RoBorregos/robocup-home/catkin_home/known_people/1.png

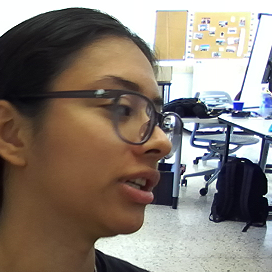
catkin_home/known_people/1.png
