RoBorregos/robocup-home/catkin_home/known_people/a0.png

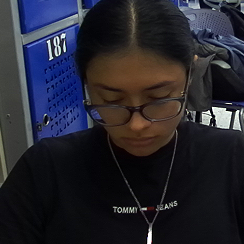
catkin_home/known_people/a0.png
