RoBorregos/robocup-home/catkin_home/known_people/adan.png

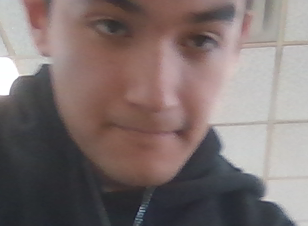
catkin_home/known_people/adan.png
