RoBorregos/robocup-home/catkin_home/known_people/ale0.png

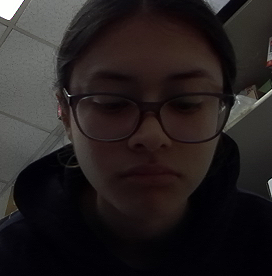
catkin_home/known_people/ale0.png
