RoBorregos/robocup-home/catkin_home/known_people/emiliano1.png

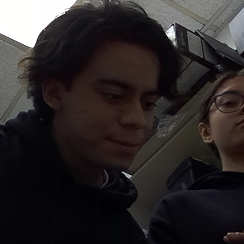
catkin_home/known_people/emiliano1.png
