RoBorregos/robocup-home/catkin_home/known_people/face0.png

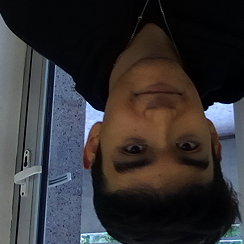
catkin_home/known_people/face0.png
