RoBorregos/robocup-home/catkin_home/known_people/face4.png

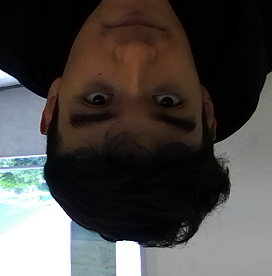
catkin_home/known_people/face4.png
