RoBorregos/robocup-home/catkin_home/known_people/iva0.png

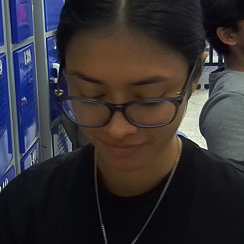
catkin_home/known_people/iva0.png
