RoBorregos/robocup-home/catkin_home/known_people/ivan0.png

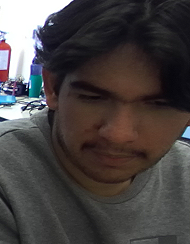
catkin_home/known_people/ivan0.png
