RoBorregos/robocup-home/catkin_home/known_people/random.png

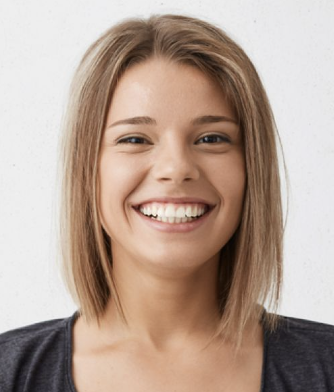
catkin_home/known_people/random.png
