RoBorregos/robocup-home/clusters.png

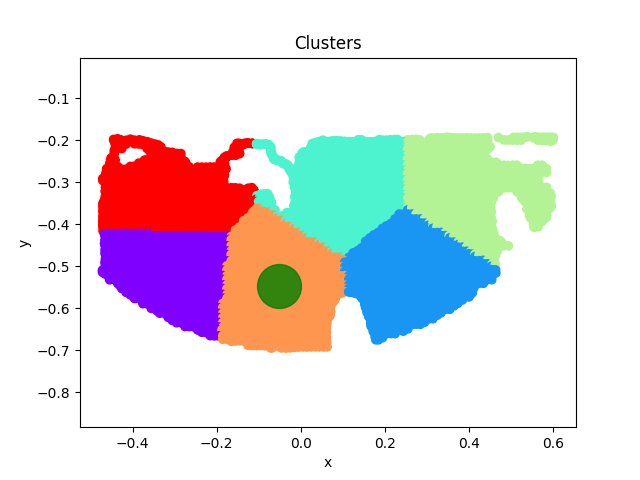
clusters.png
