RoBorregos/robocup-home/catkin_home/src/robot_description/meshes/GripperSF/Base_Gripper.STL

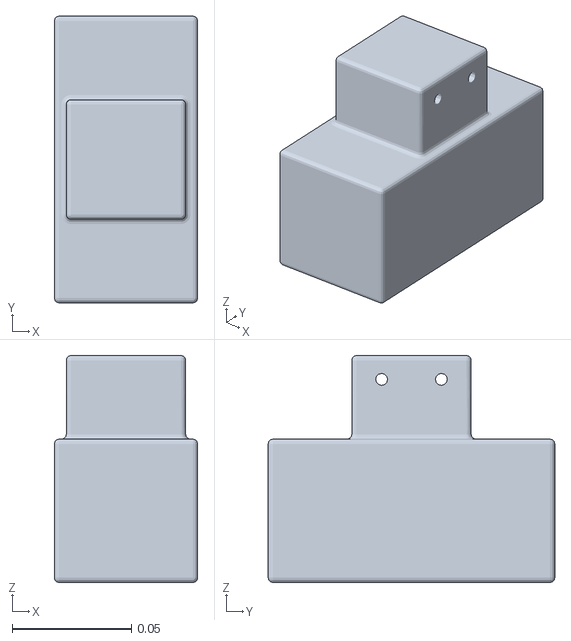
[picture p31: CAD file, 2023-06-28]
catkin_home/src/robot_description/meshes/GripperSF/Base_Gripper.STL
0.06 x 0.12 x 0.095
