RoBorregos/robocup-home/catkin_home/src/robot_description/meshes/Dashgo/BaseSinPalo.stl

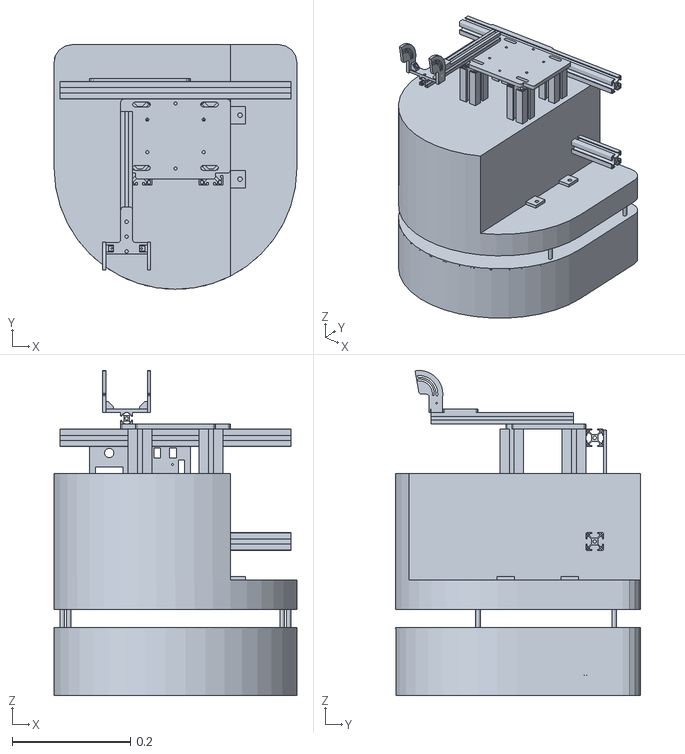
[picture p32: CAD file, 2023-11-25]
catkin_home/src/robot_description/meshes/Dashgo/BaseSinPalo.stl
0.41 x 0.413 x 0.549
