RoBorregos/robocup-home/catkin_home/src/robot_description/meshes/Garra_I.STL

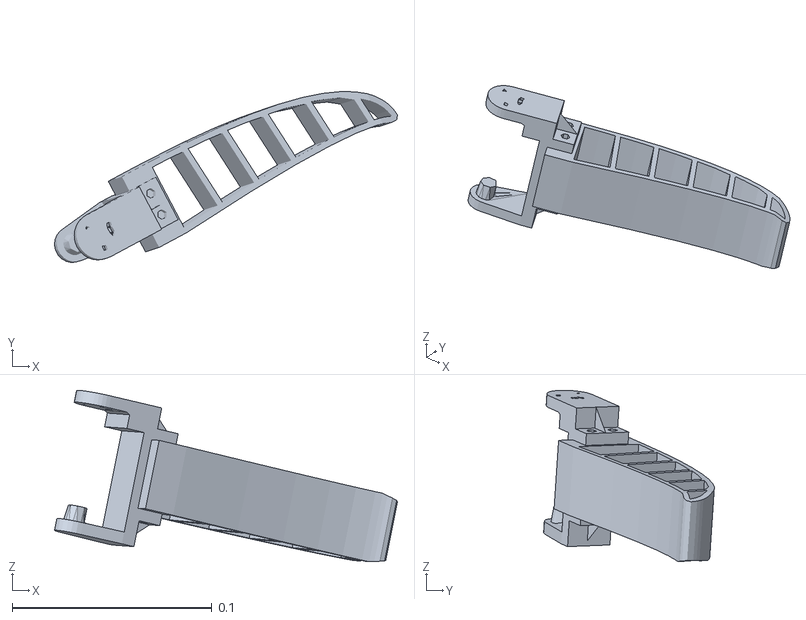
[picture p33: CAD file, 2022-05-05]
catkin_home/src/robot_description/meshes/Garra_I.STL
0.172 x 0.0855 x 0.0858
