RoBorregos/robocup-home/catkin_home/src/robot_description/meshes/BASE_PINZA.STL

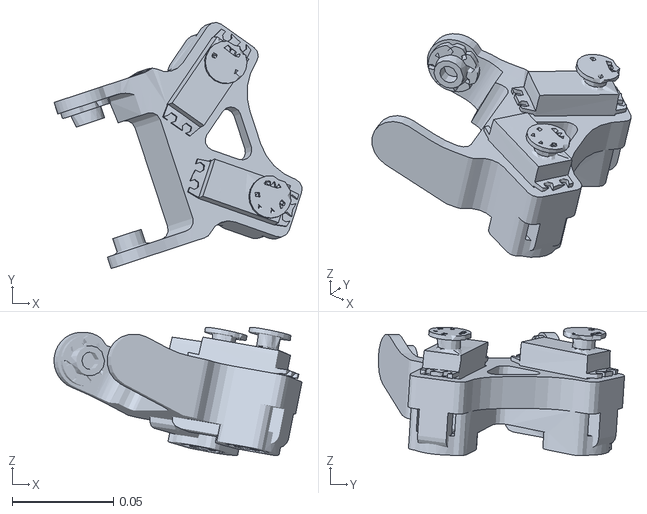
[picture p34: CAD file, 2022-05-05]
catkin_home/src/robot_description/meshes/BASE_PINZA.STL
0.123 x 0.122 x 0.0635
