RoBorregos/robocup-home/catkin_home/src/robot_description/meshes/Dashgo/BaseCollisionsSinPalo.stl

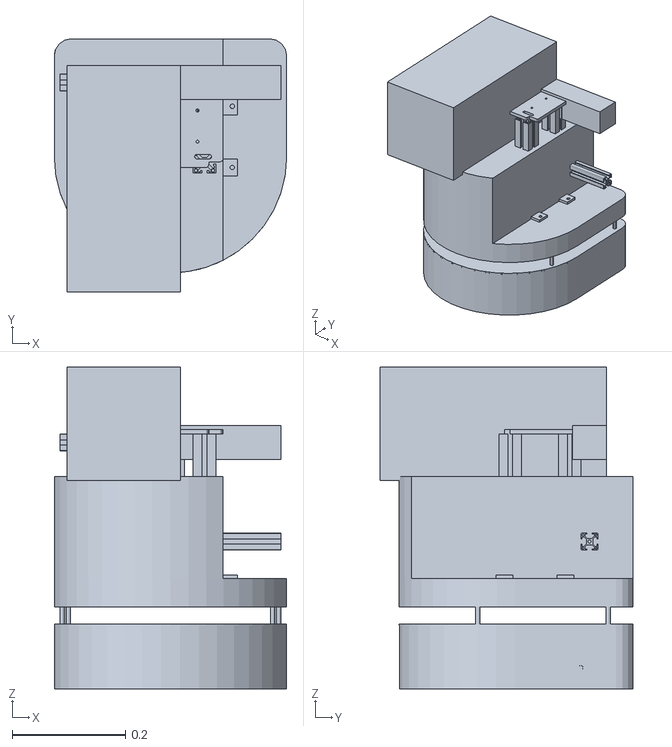
[picture p35: CAD file, 2023-11-25]
catkin_home/src/robot_description/meshes/Dashgo/BaseCollisionsSinPalo.stl
0.41 x 0.447 x 0.568
