RoBorregos/robocup-home/object_detection/images/test/IMG_9574.jpg

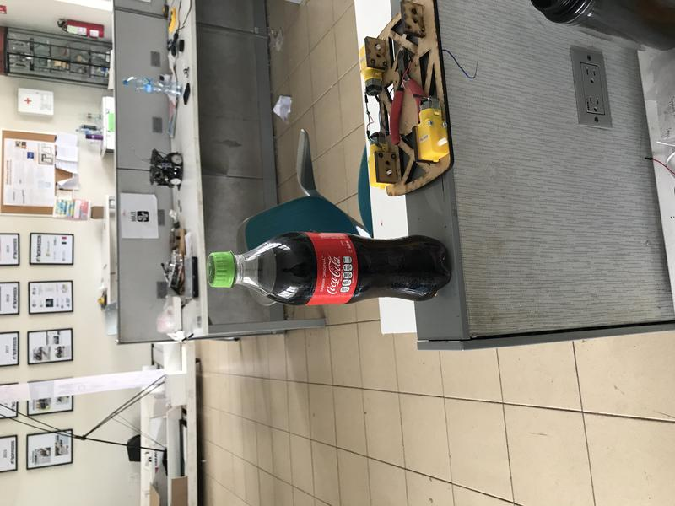
object_detection/images/test/IMG_9574.jpg
