RoBorregos/robocup-home/object_detection/images/test/IMG_9580.jpg

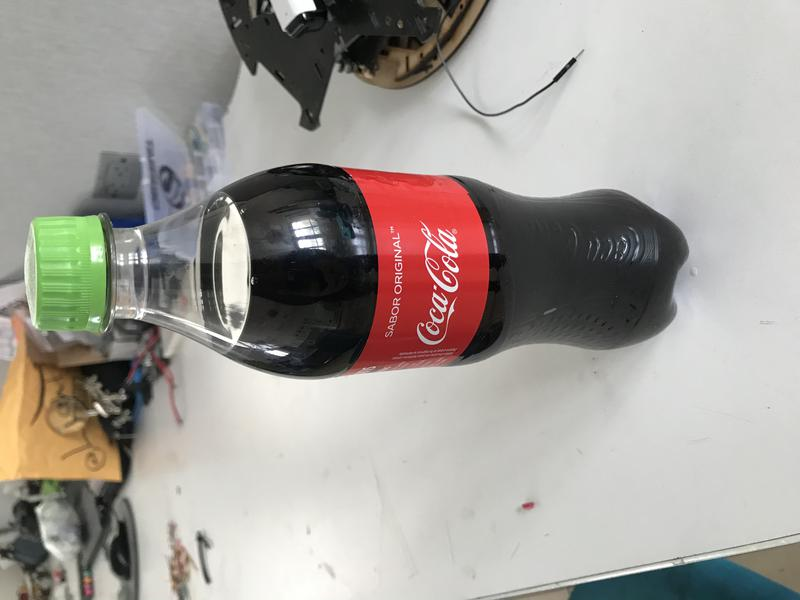
object_detection/images/test/IMG_9580.jpg
