RoBorregos/robocup-home/object_detection/images/test/IMG_9582.jpg

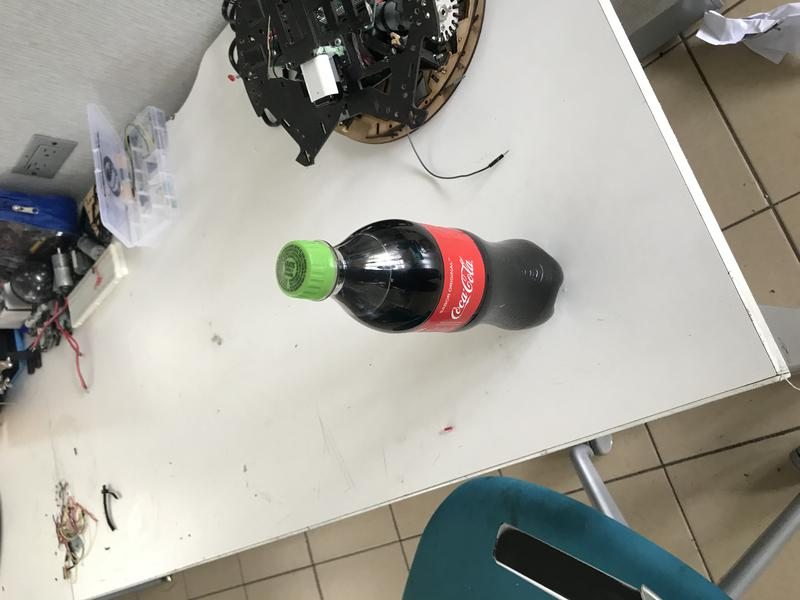
object_detection/images/test/IMG_9582.jpg
