RoBorregos/robocup-home/object_detection/images/test/IMG_9587.jpg

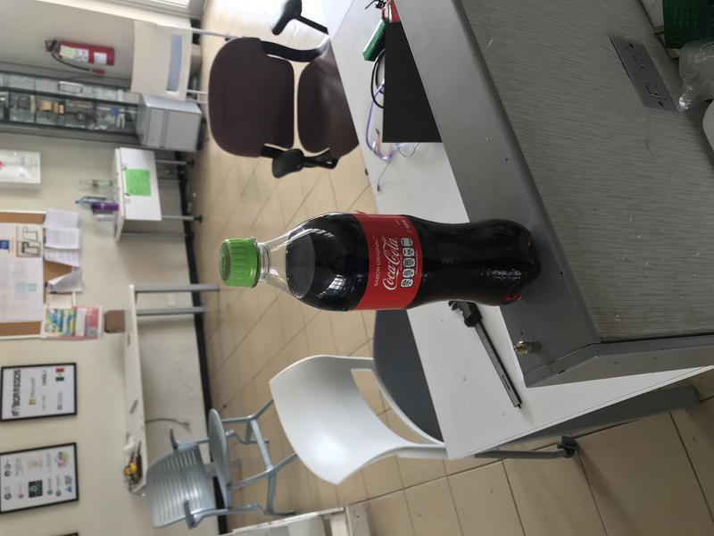
object_detection/images/test/IMG_9587.jpg
