RoBorregos/robocup-home/object_detection/images/test/IMG_9591.jpg

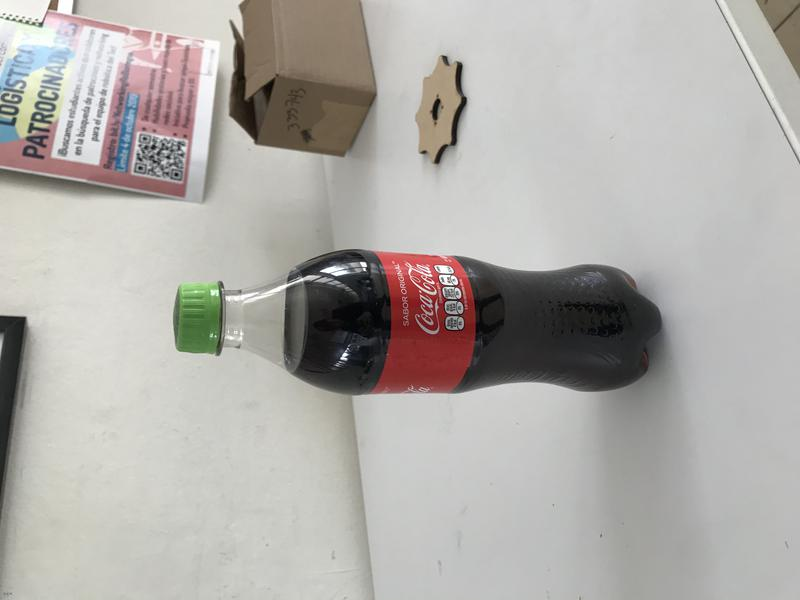
object_detection/images/test/IMG_9591.jpg
