RoBorregos/robocup-home/object_detection/images/test/IMG_9599.jpg

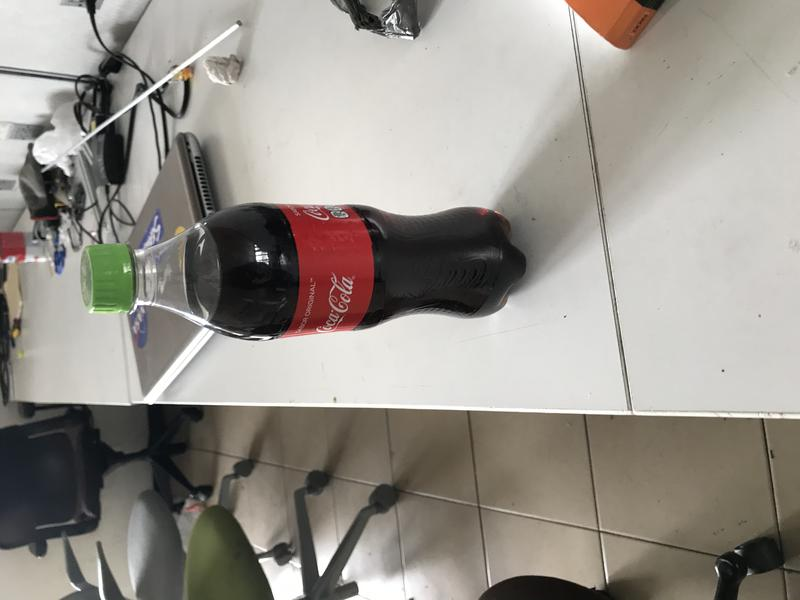
object_detection/images/test/IMG_9599.jpg
