RoBorregos/robocup-home/object_detection/images/test/IMG_9605.jpg

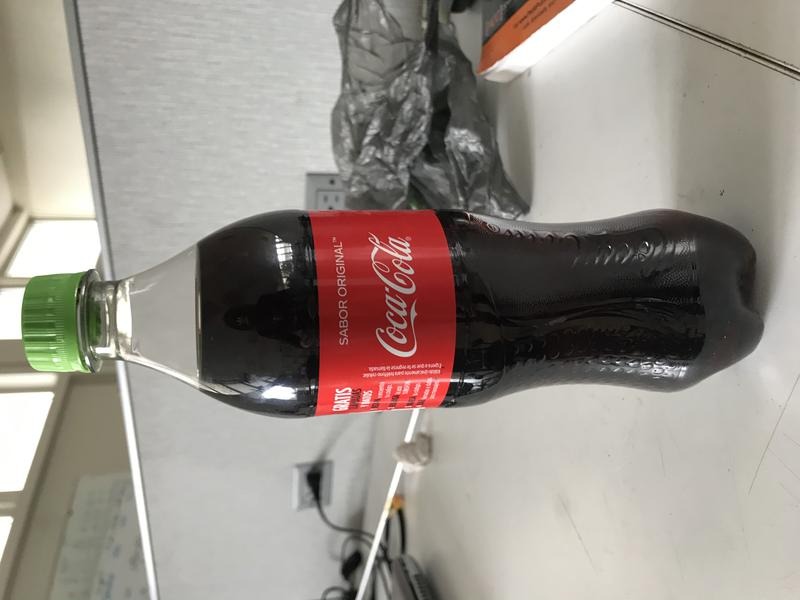
object_detection/images/test/IMG_9605.jpg
