RoBorregos/robocup-home/object_detection/images/test/IMG_9612.jpg

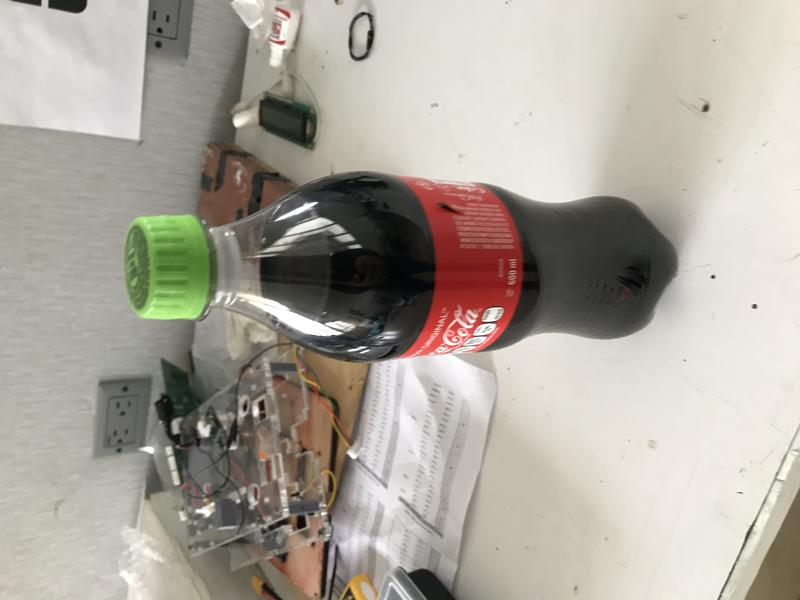
object_detection/images/test/IMG_9612.jpg
