RoBorregos/robocup-home/object_detection/images/test/IMG_9617.jpg

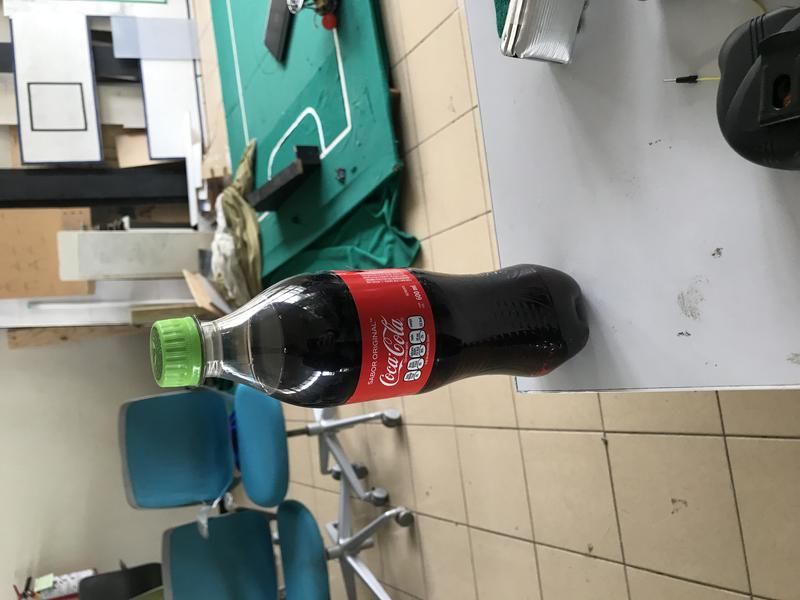
object_detection/images/test/IMG_9617.jpg
