RoBorregos/robocup-home/object_detection/images/test/IMG_9623.jpg

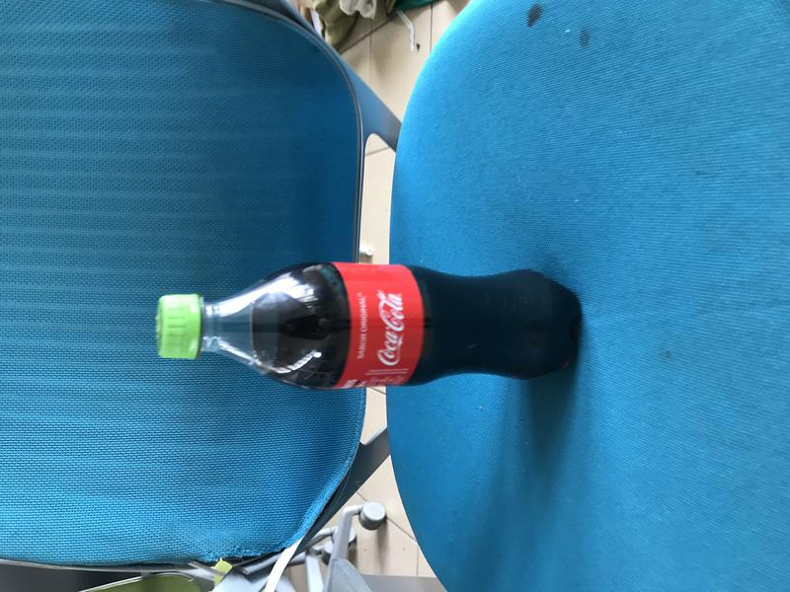
object_detection/images/test/IMG_9623.jpg
