RoBorregos/robocup-home/object_detection/images/test/IMG_9628.jpg

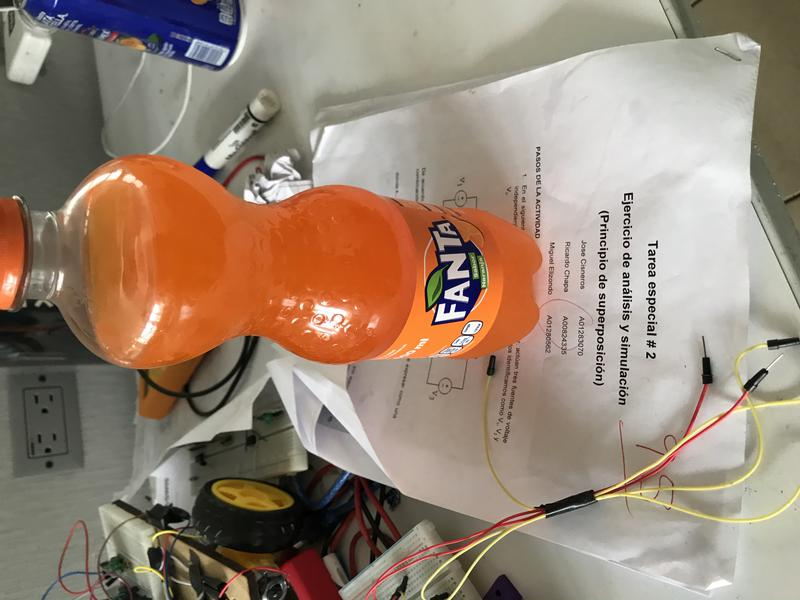
object_detection/images/test/IMG_9628.jpg
