RoBorregos/robocup-home/object_detection/images/test/IMG_9636.jpg

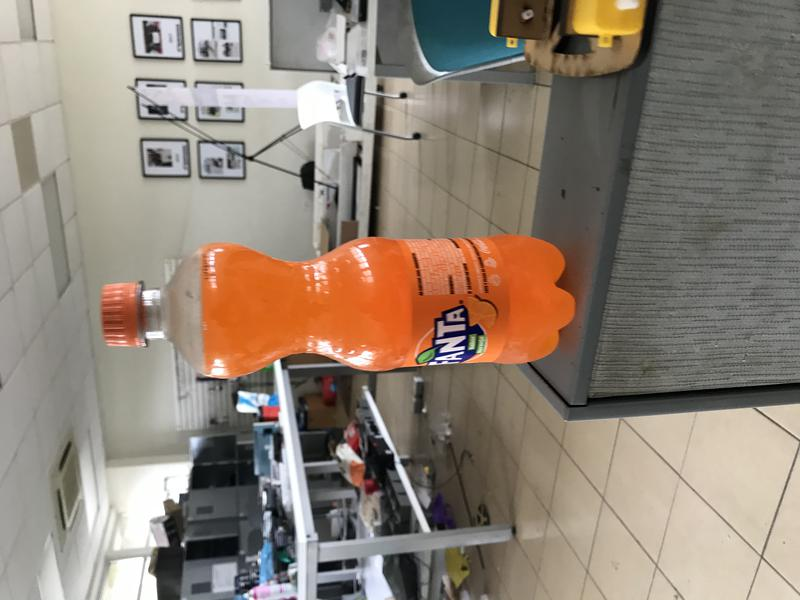
object_detection/images/test/IMG_9636.jpg
