RoBorregos/robocup-home/object_detection/images/test/IMG_9645.jpg

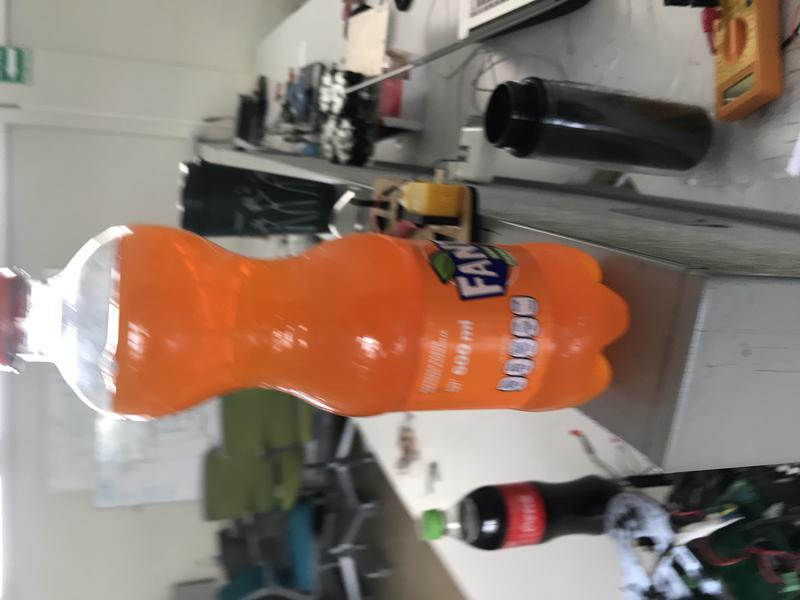
object_detection/images/test/IMG_9645.jpg
