RoBorregos/robocup-home/object_detection/images/test/IMG_9652.jpg

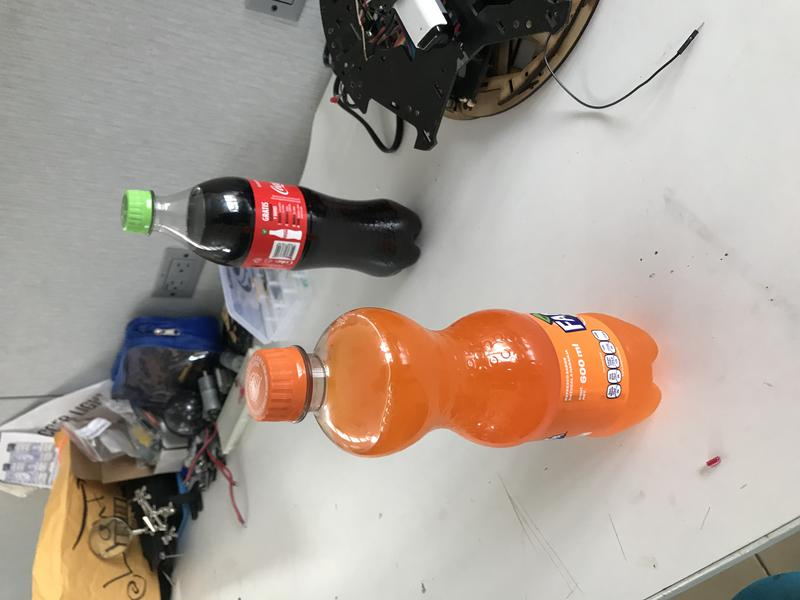
object_detection/images/test/IMG_9652.jpg
