RoBorregos/robocup-home/object_detection/images/test/IMG_9660.jpg

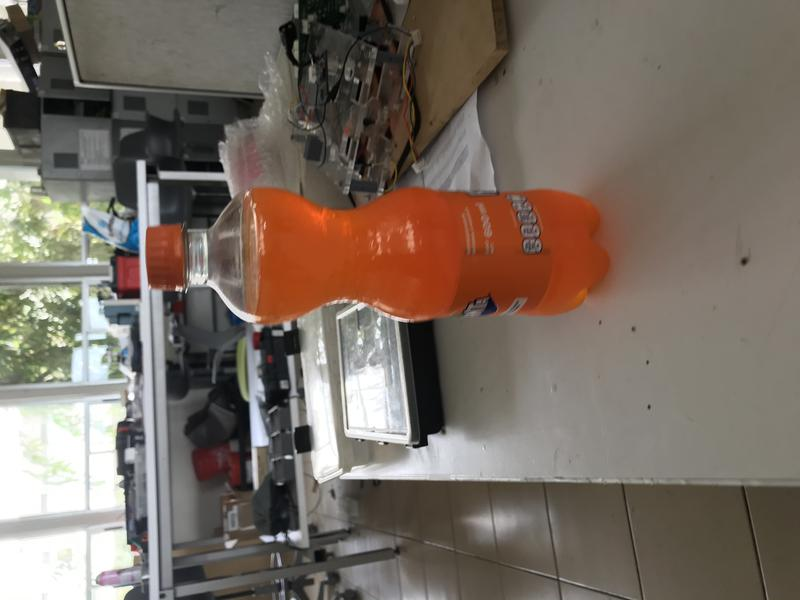
object_detection/images/test/IMG_9660.jpg
