RoBorregos/robocup-home/object_detection/images/test/IMG_9667.jpg

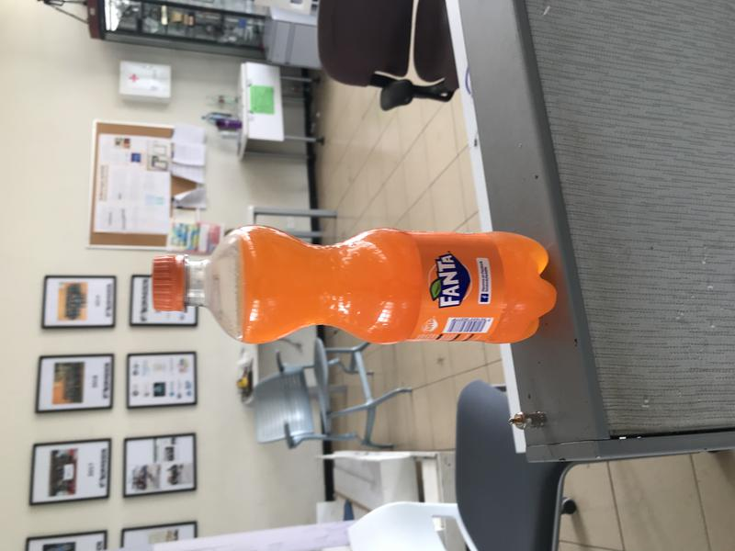
object_detection/images/test/IMG_9667.jpg
