RoBorregos/robocup-home/object_detection/images/test/IMG_9672.jpg

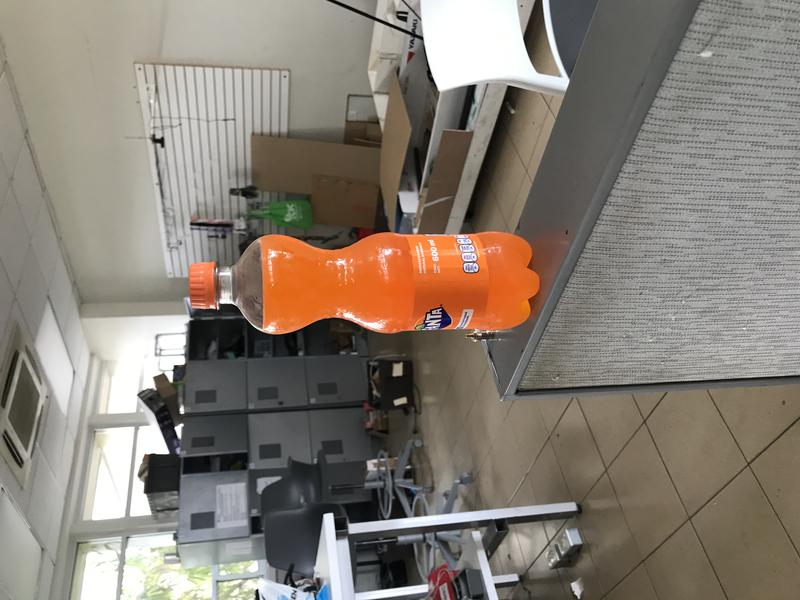
object_detection/images/test/IMG_9672.jpg
