RoBorregos/robocup-home/object_detection/images/test/IMG_9680.jpg

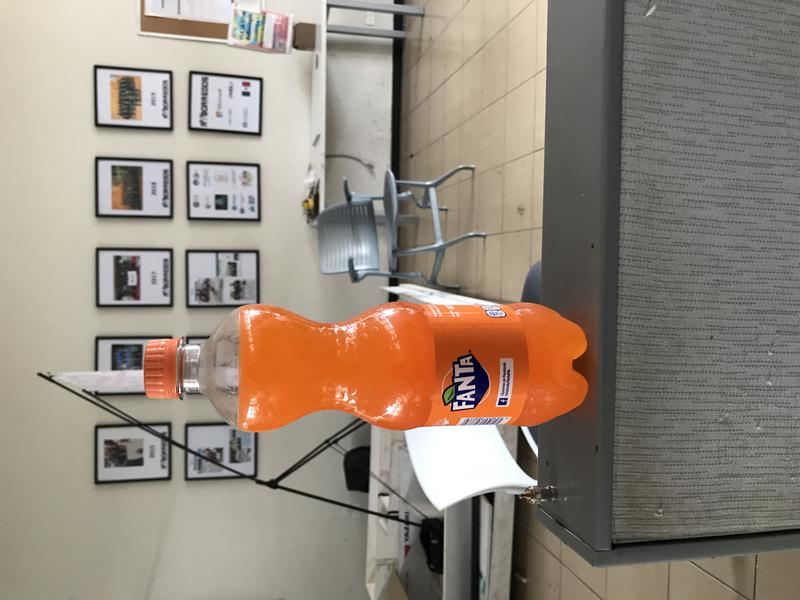
object_detection/images/test/IMG_9680.jpg
