RoBorregos/robocup-home/object_detection/images/test/IMG_9692.jpg

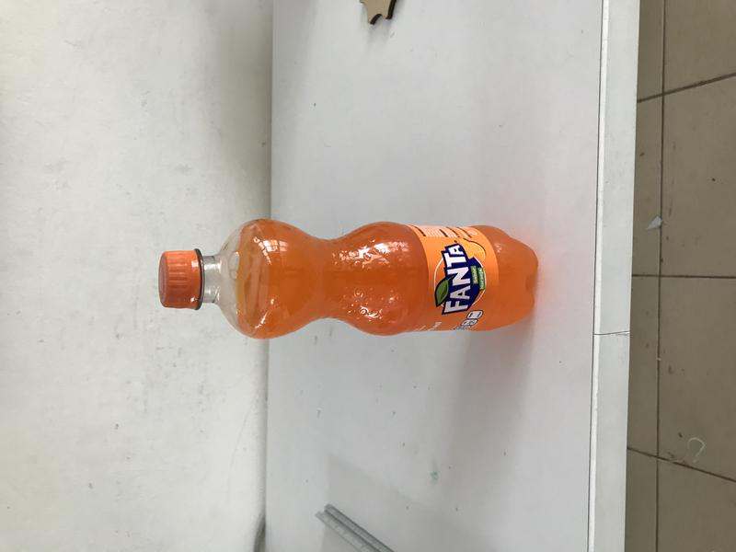
object_detection/images/test/IMG_9692.jpg
