RoBorregos/robocup-home/object_detection/images/test/IMG_9703.jpg

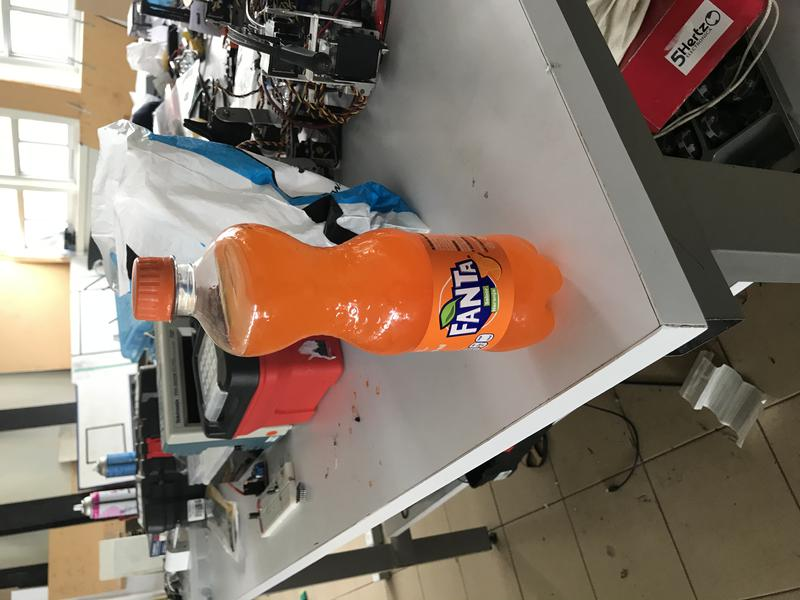
object_detection/images/test/IMG_9703.jpg
