RoBorregos/robocup-home/object_detection/images/test/IMG_9719.jpg

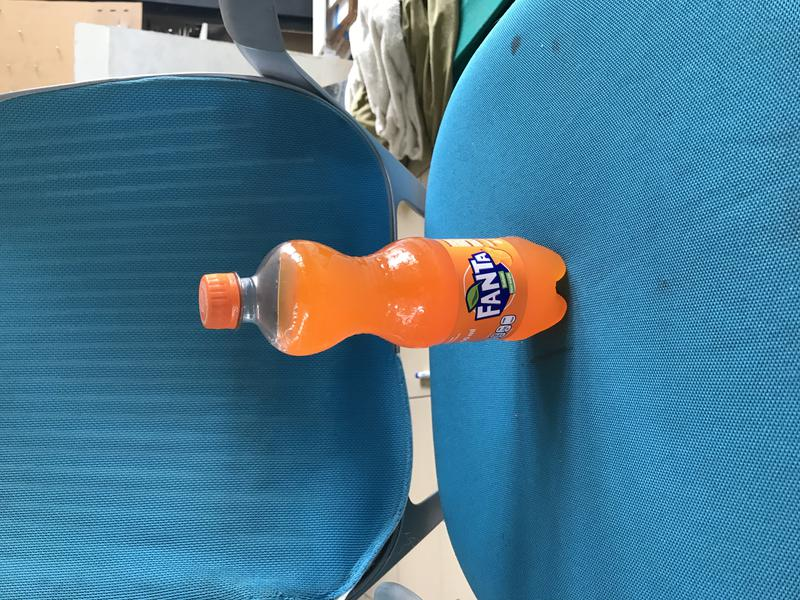
object_detection/images/test/IMG_9719.jpg
