RoBorregos/robocup-home/object_detection/images/test/IMG_9730.jpg

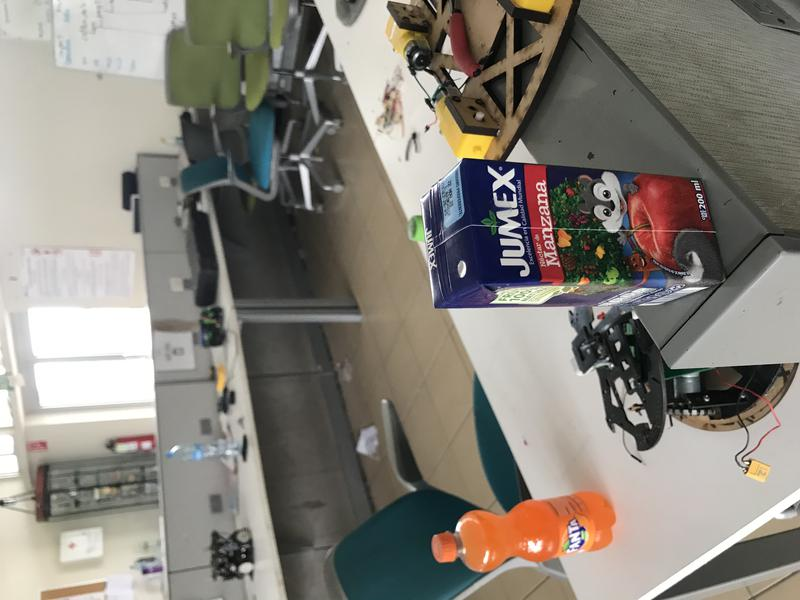
object_detection/images/test/IMG_9730.jpg
