RoBorregos/robocup-home/object_detection/images/test/IMG_9737.jpg

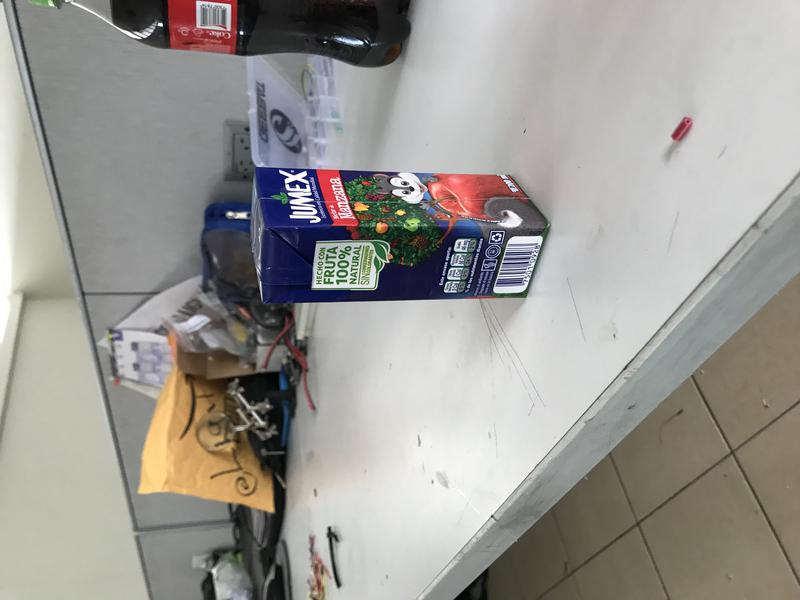
object_detection/images/test/IMG_9737.jpg
