RoBorregos/robocup-home/object_detection/images/test/IMG_9745.jpg

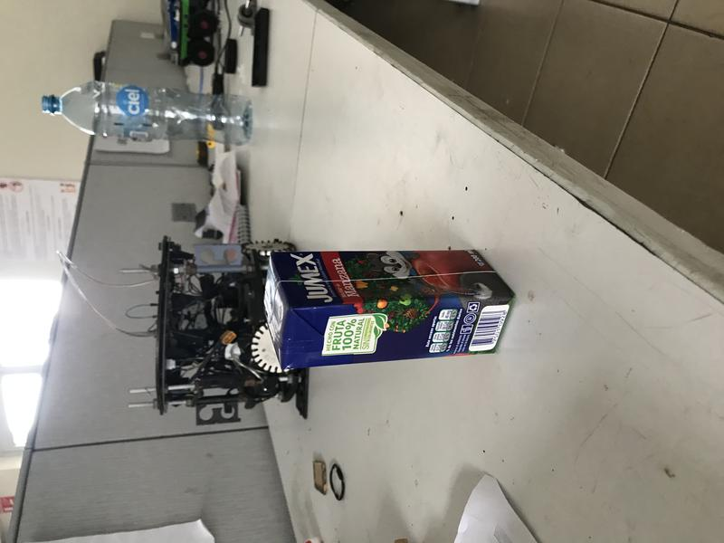
object_detection/images/test/IMG_9745.jpg
