RoBorregos/robocup-home/object_detection/images/test/IMG_9752.jpg

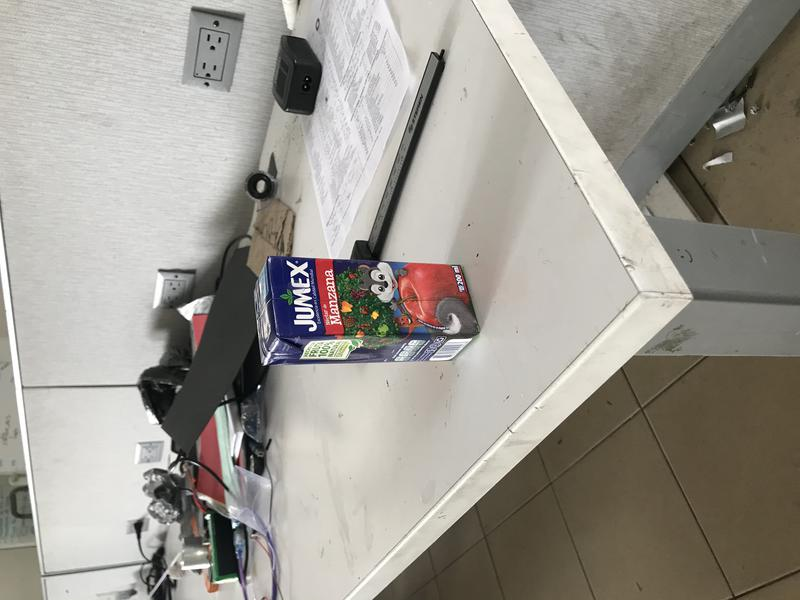
object_detection/images/test/IMG_9752.jpg
