RoBorregos/robocup-home/object_detection/images/test/IMG_9754.jpg

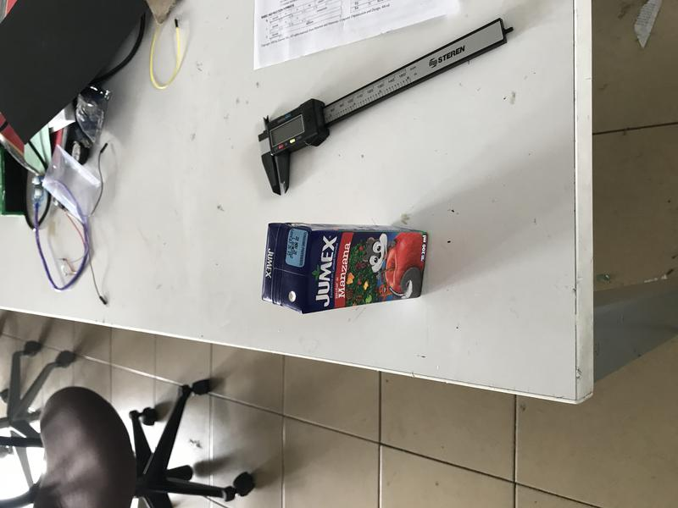
object_detection/images/test/IMG_9754.jpg
