RoBorregos/robocup-home/object_detection/images/test/IMG_9758.jpg

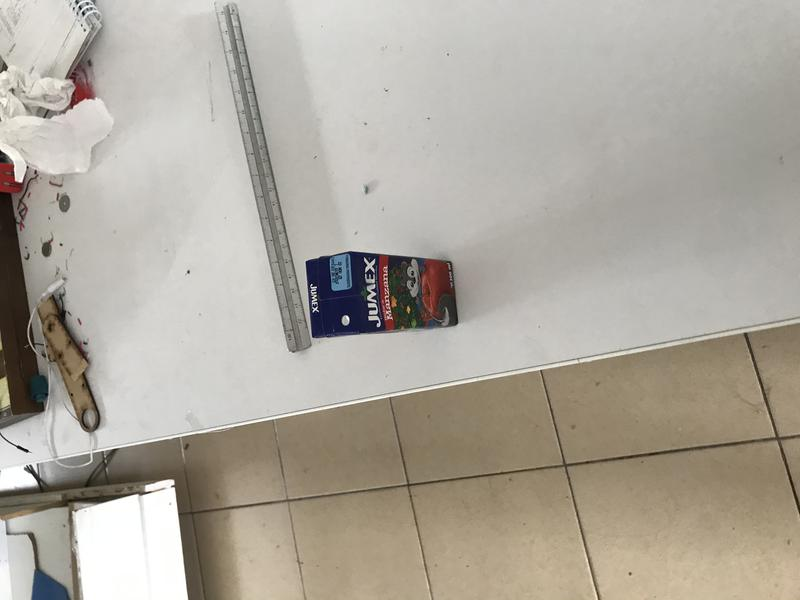
object_detection/images/test/IMG_9758.jpg
