RoBorregos/robocup-home/object_detection/images/test/IMG_9762.jpg

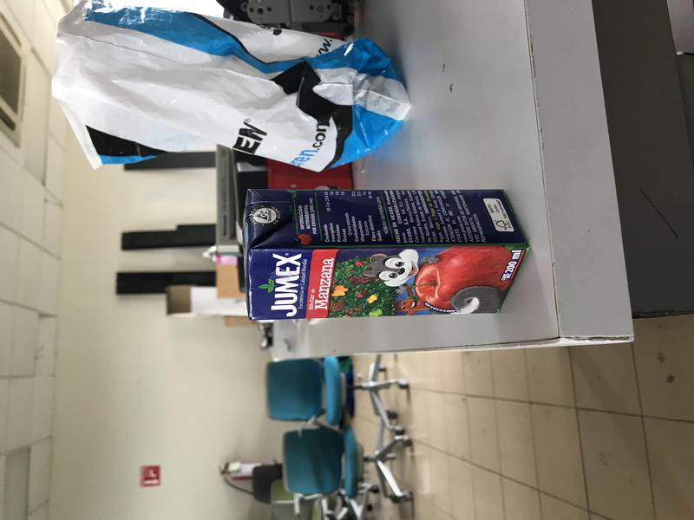
object_detection/images/test/IMG_9762.jpg
