RoBorregos/robocup-home/object_detection/images/test/IMG_9765.jpg

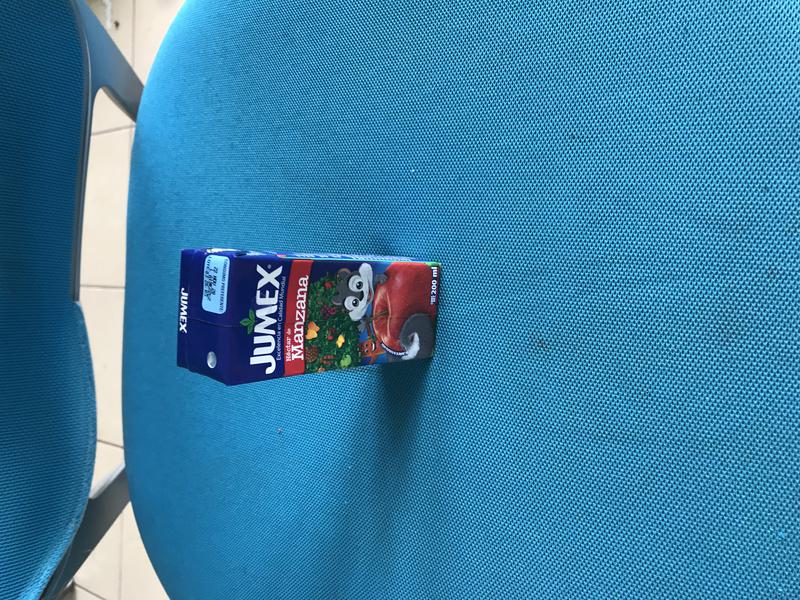
object_detection/images/test/IMG_9765.jpg
