RoBorregos/robocup-home/object_detection/images/test/IMG_9771.jpg

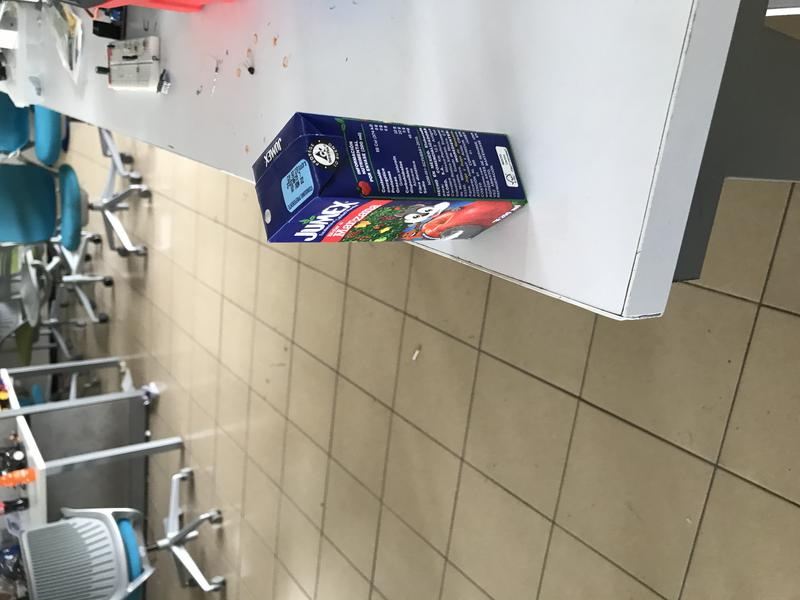
object_detection/images/test/IMG_9771.jpg
