RoBorregos/robocup-home/object_detection/images/test/IMG_9773.jpg

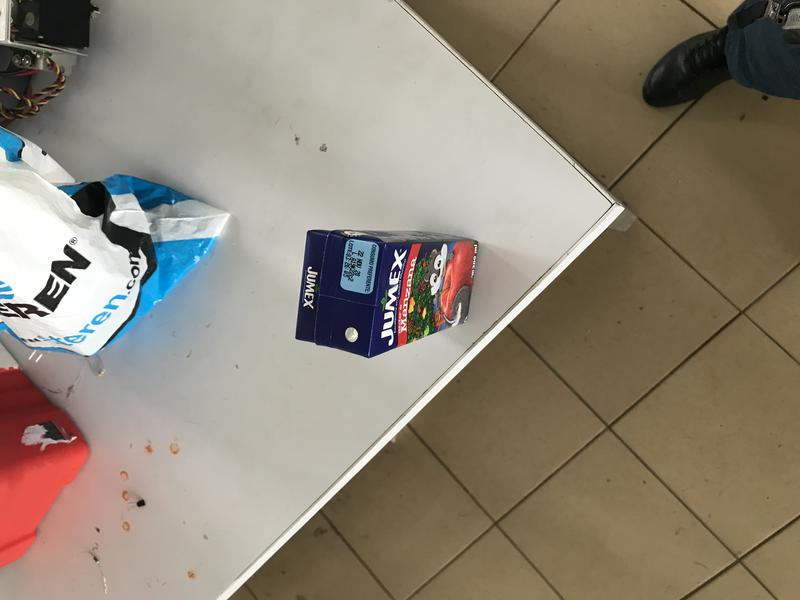
object_detection/images/test/IMG_9773.jpg
