RoBorregos/robocup-home/object_detection/images/test/IMG_9781.jpg

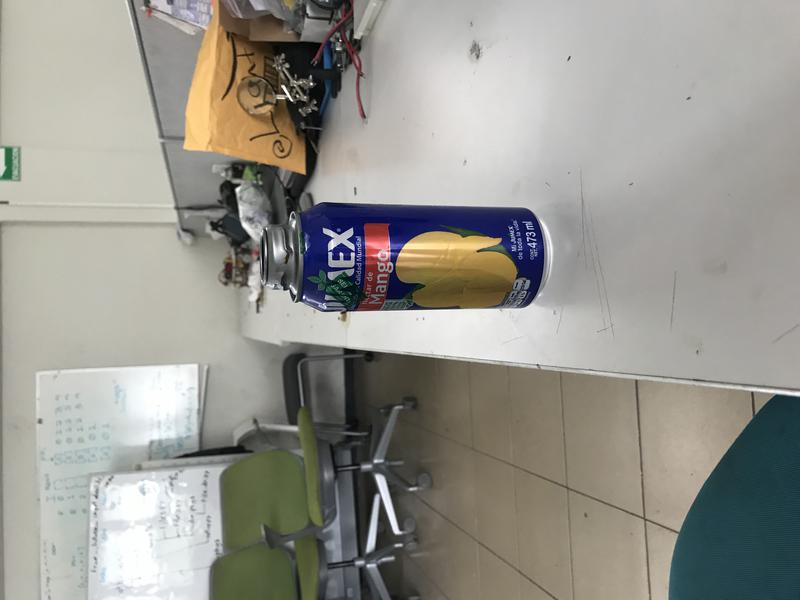
object_detection/images/test/IMG_9781.jpg
