RoBorregos/robocup-home/object_detection/images/test/IMG_9785.jpg

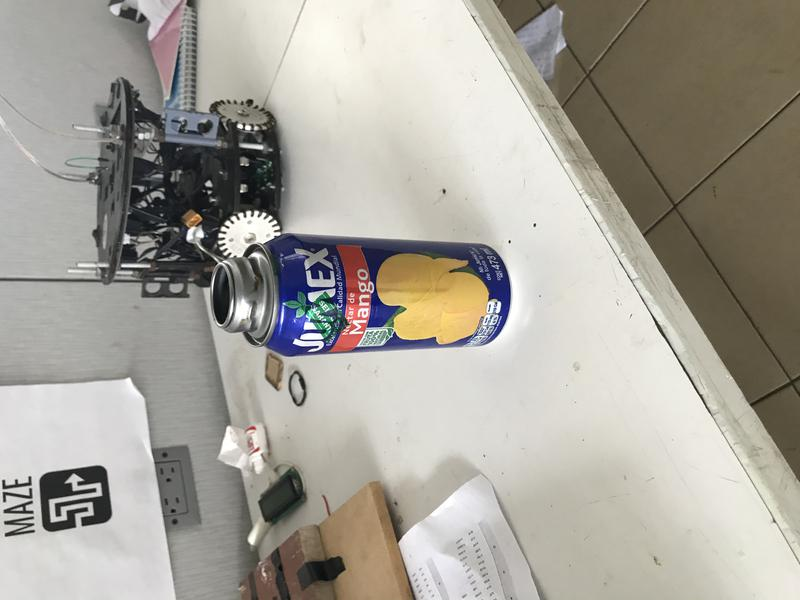
object_detection/images/test/IMG_9785.jpg
