RoBorregos/robocup-home/object_detection/images/test/IMG_9788.jpg

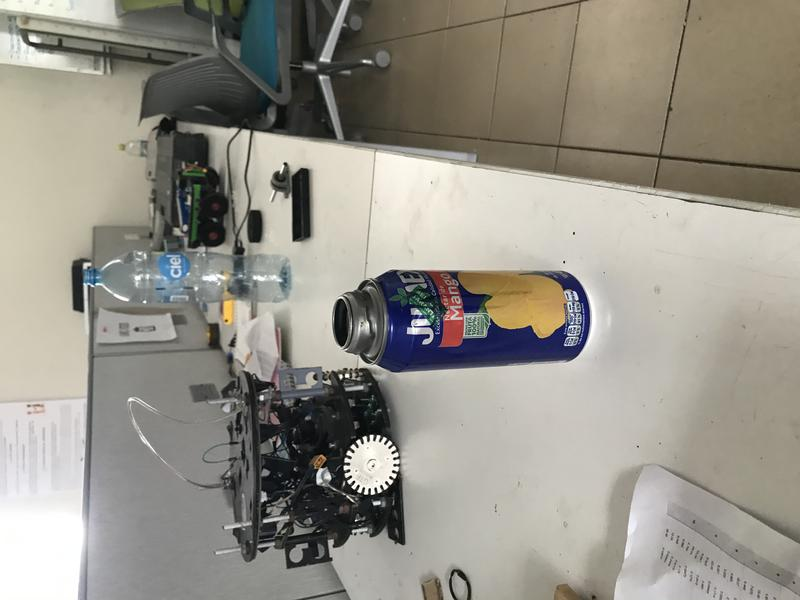
object_detection/images/test/IMG_9788.jpg
