RoBorregos/robocup-home/object_detection/images/test/IMG_9790.jpg

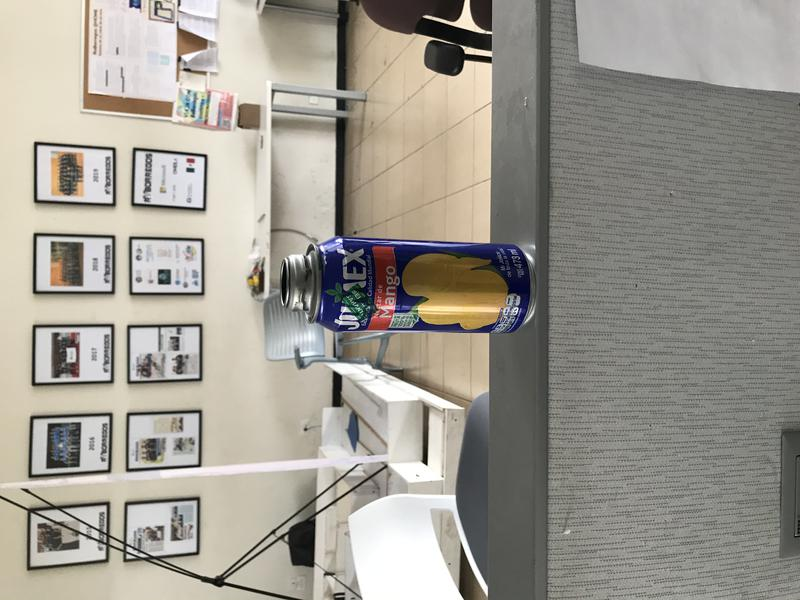
object_detection/images/test/IMG_9790.jpg
