RoBorregos/robocup-home/object_detection/images/test/IMG_9796.jpg

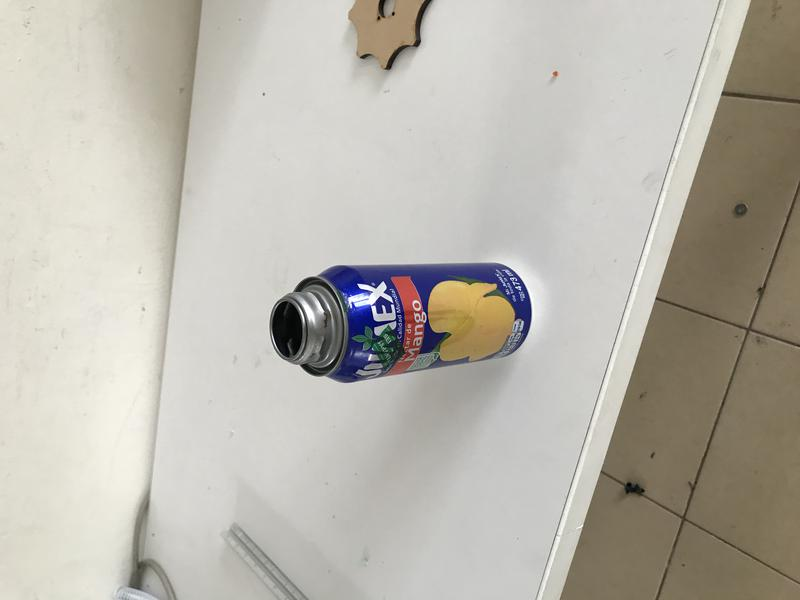
object_detection/images/test/IMG_9796.jpg
