RoBorregos/robocup-home/object_detection/images/test/IMG_9800.jpg

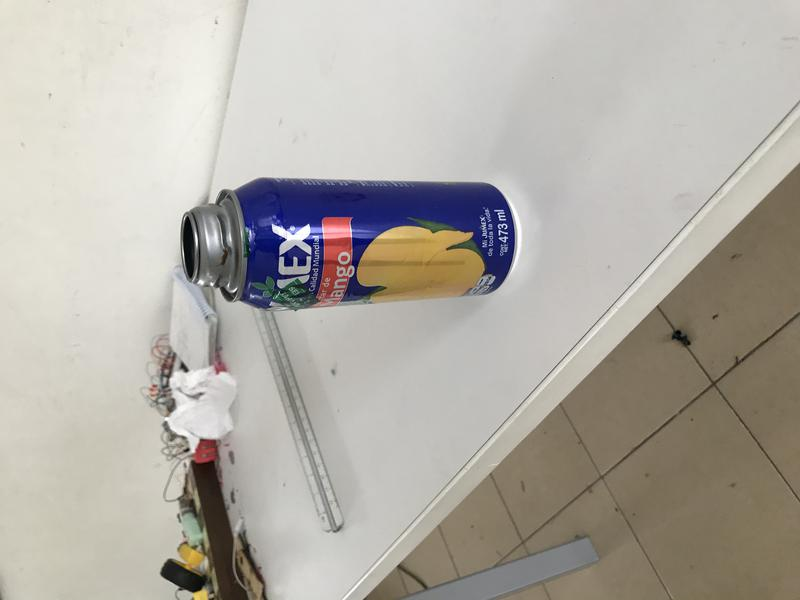
object_detection/images/test/IMG_9800.jpg
