RoBorregos/robocup-home/object_detection/images/test/IMG_9806.jpg

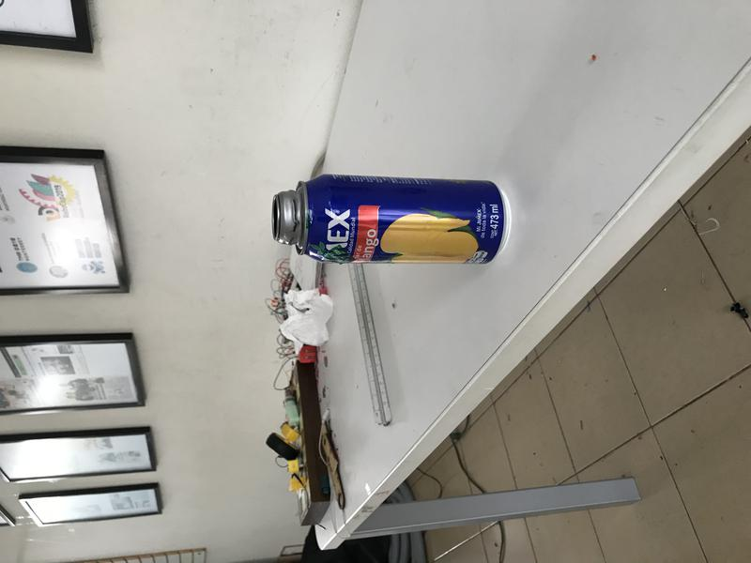
object_detection/images/test/IMG_9806.jpg
