RoBorregos/robocup-home/object_detection/images/test/IMG_9808.jpg

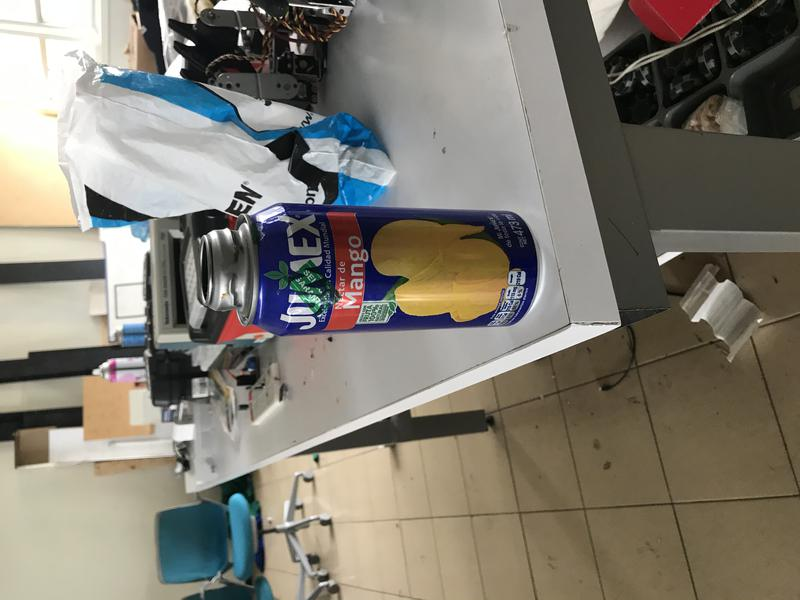
object_detection/images/test/IMG_9808.jpg
