RoBorregos/robocup-home/object_detection/images/test/IMG_9810.jpg

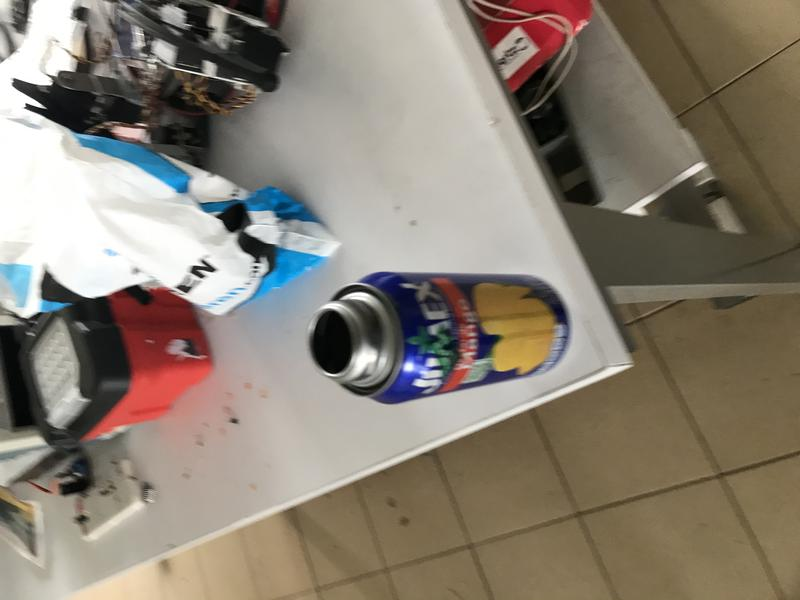
object_detection/images/test/IMG_9810.jpg
