RoBorregos/robocup-home/object_detection/images/test/IMG_9816.jpg

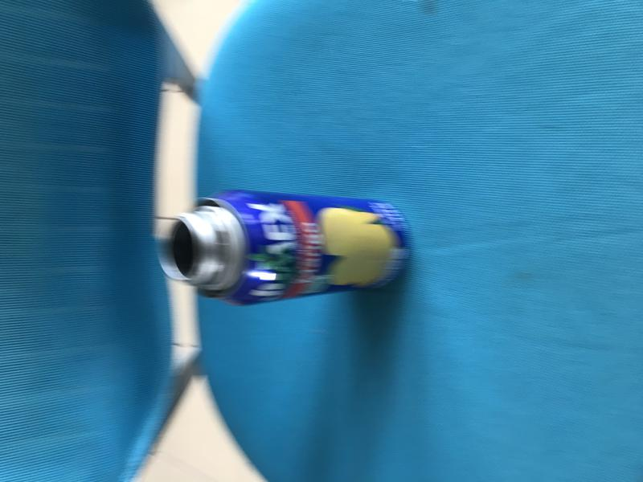
object_detection/images/test/IMG_9816.jpg
