RoBorregos/robocup-home/object_detection/images/test/IMG_9823.jpg

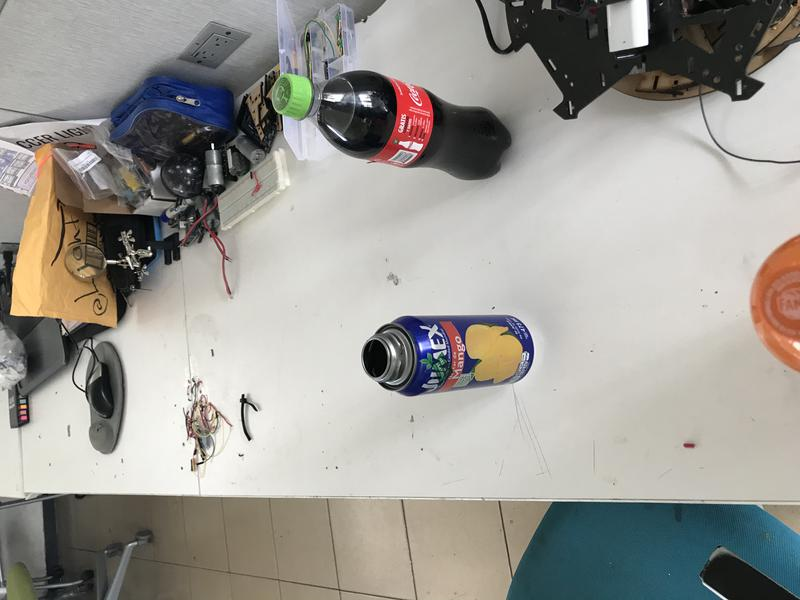
object_detection/images/test/IMG_9823.jpg
