RoBorregos/robocup-home/object_detection/images/test/IMG_9825.jpg

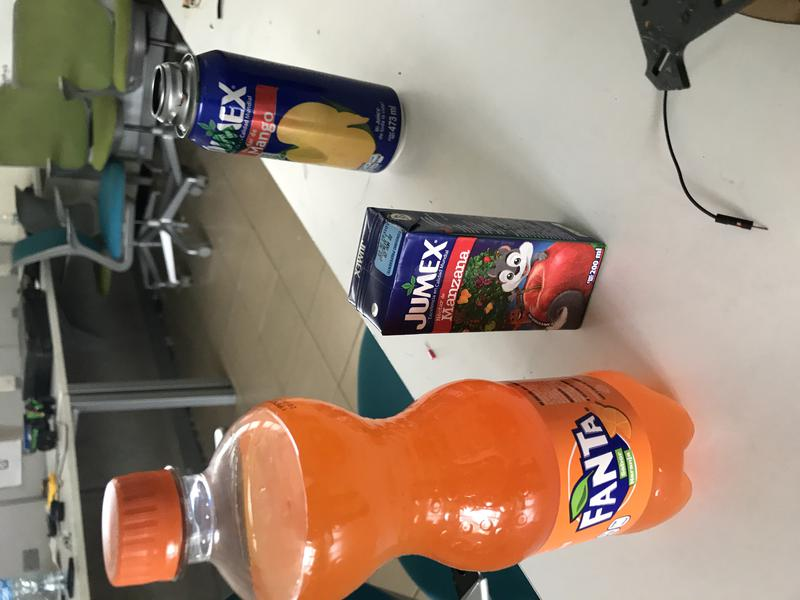
object_detection/images/test/IMG_9825.jpg
