RoBorregos/robocup-home/object_detection/images/test/IMG_9829.jpg

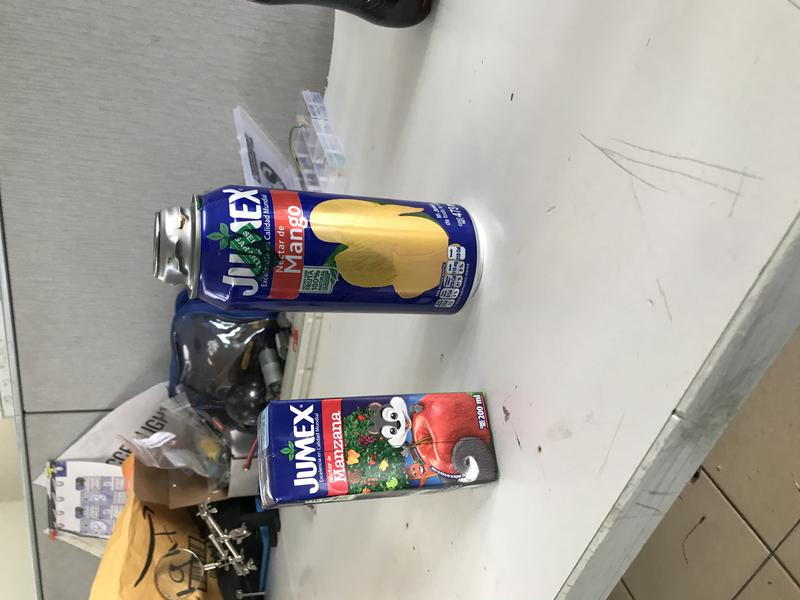
object_detection/images/test/IMG_9829.jpg
