RoBorregos/robocup-home/object_detection/images/test/IMG_9836.jpg

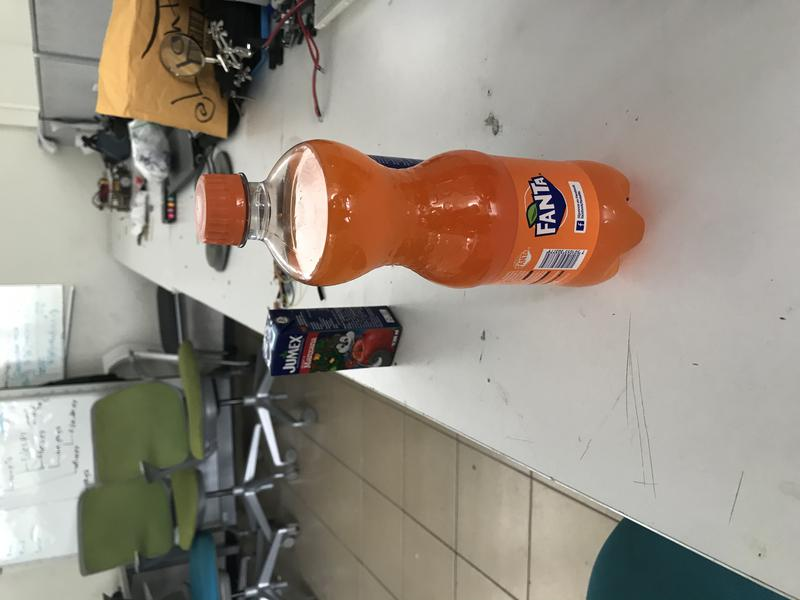
object_detection/images/test/IMG_9836.jpg
