RoBorregos/robocup-home/object_detection/images/test/IMG_9841.jpg

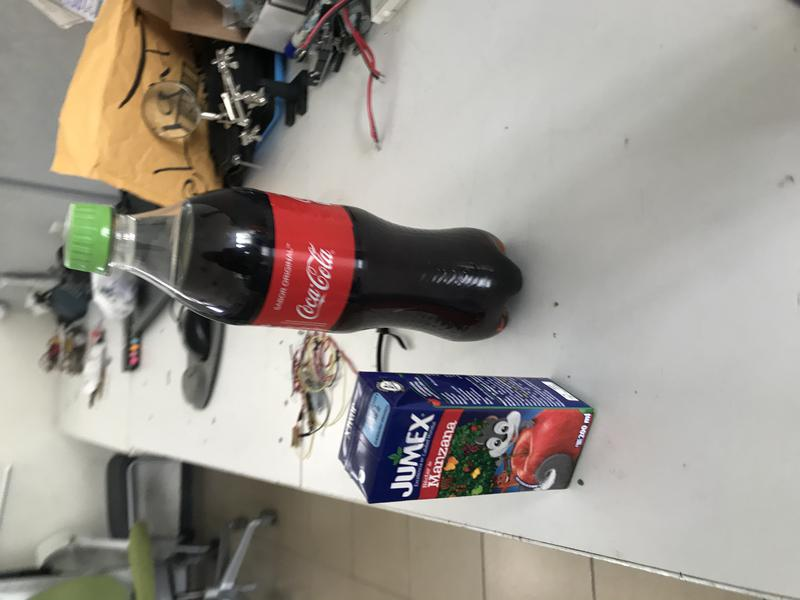
object_detection/images/test/IMG_9841.jpg
