RoBorregos/robocup-home/object_detection/images/test/IMG_9849.jpg

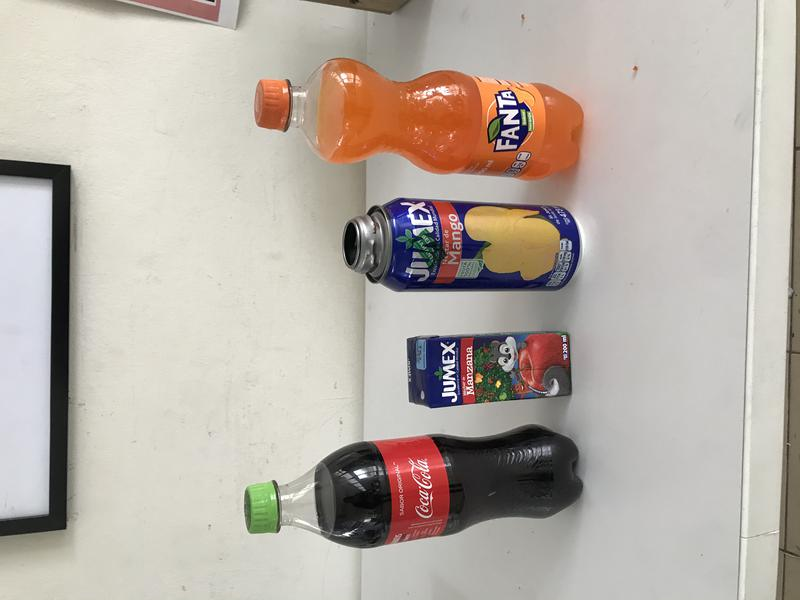
object_detection/images/test/IMG_9849.jpg
