RoBorregos/robocup-home/object_detection/test_images/image1.jpg

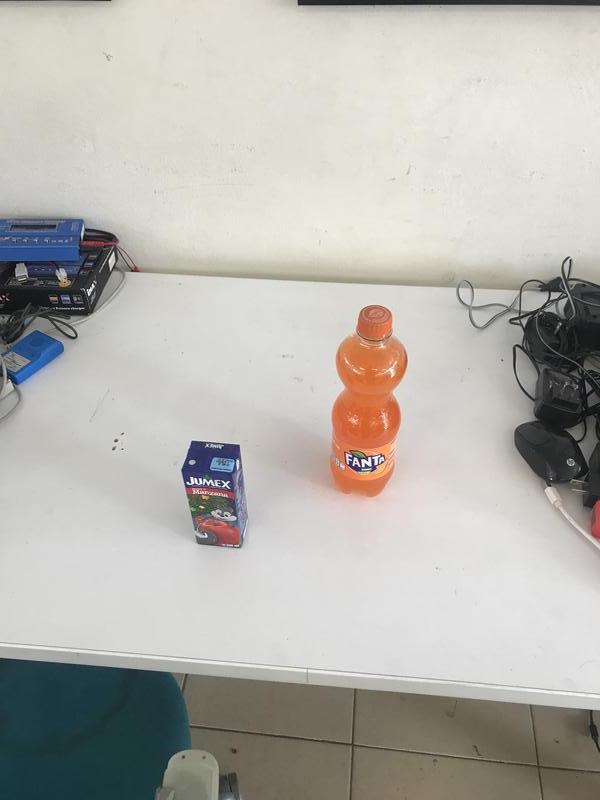
object_detection/test_images/image1.jpg
