RoBorregos/robocup-home/object_detection/test_images/image2.jpg

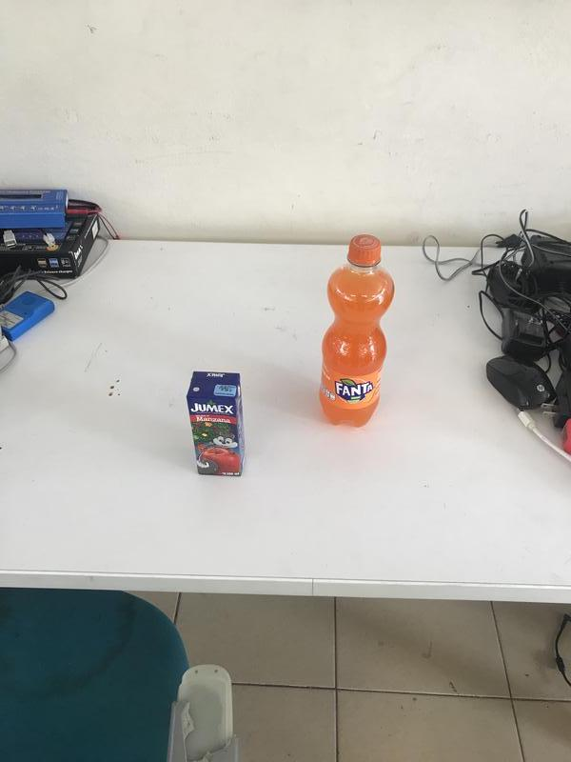
object_detection/test_images/image2.jpg
