RoBorregos/robocup-home/object_detection/test_images/image3.jpg

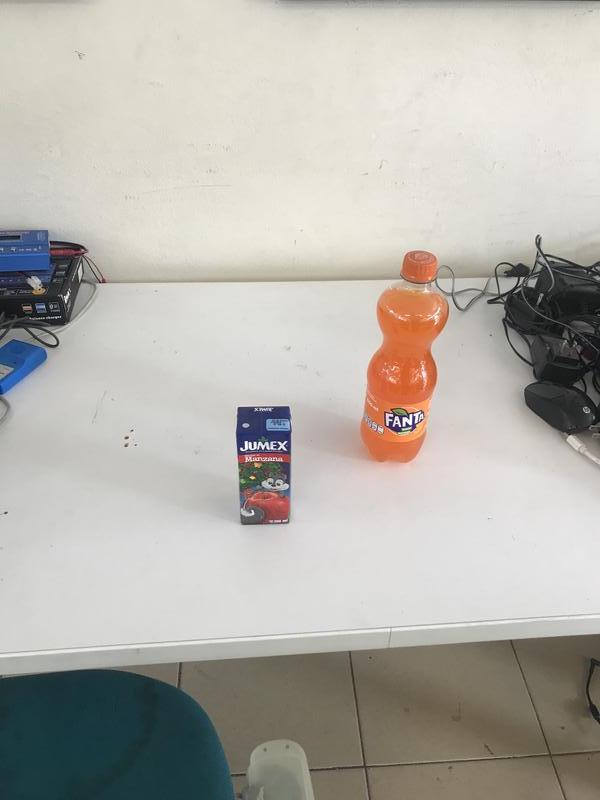
object_detection/test_images/image3.jpg
