RoBorregos/robocup-home/object_detection/test_images/image4.jpg

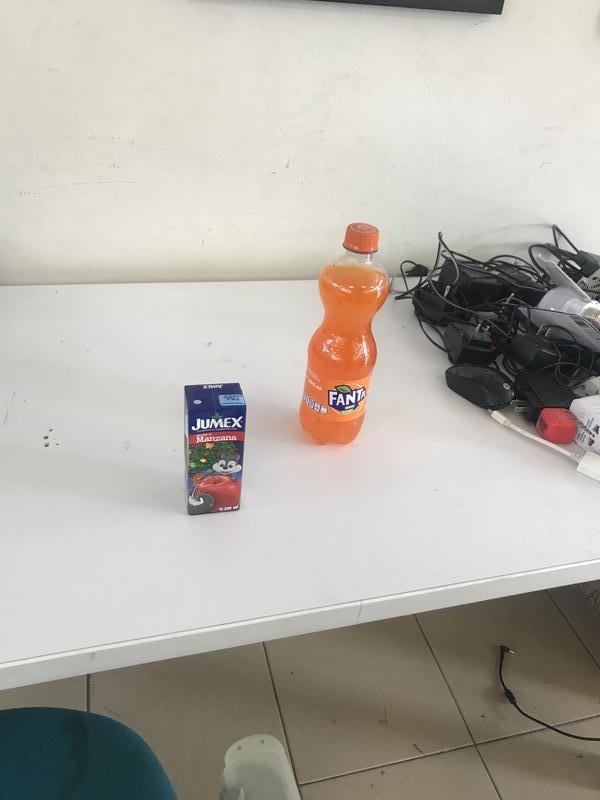
object_detection/test_images/image4.jpg
