RoBorregos/robocup-home/object_detection/test_images/image5.jpg

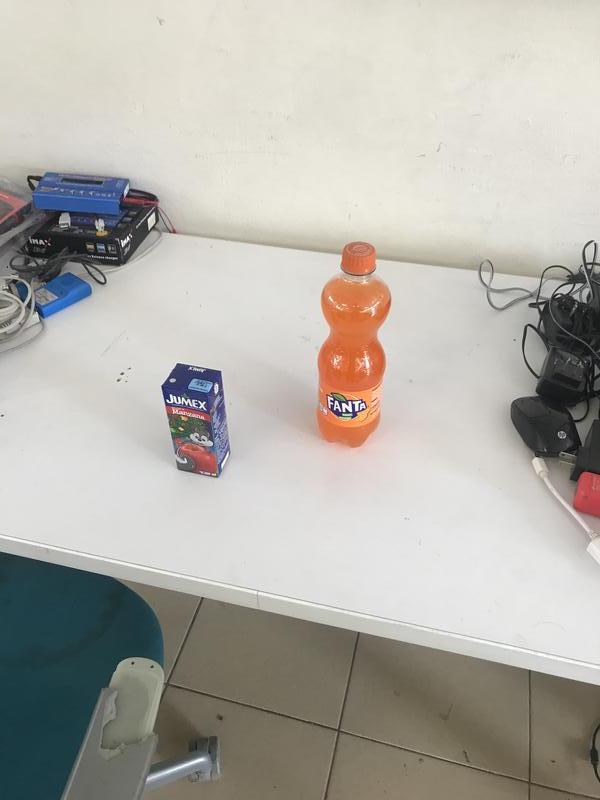
object_detection/test_images/image5.jpg
