RoBorregos/robocup-home/object_detection/test_images/test_image_tf2.jpg

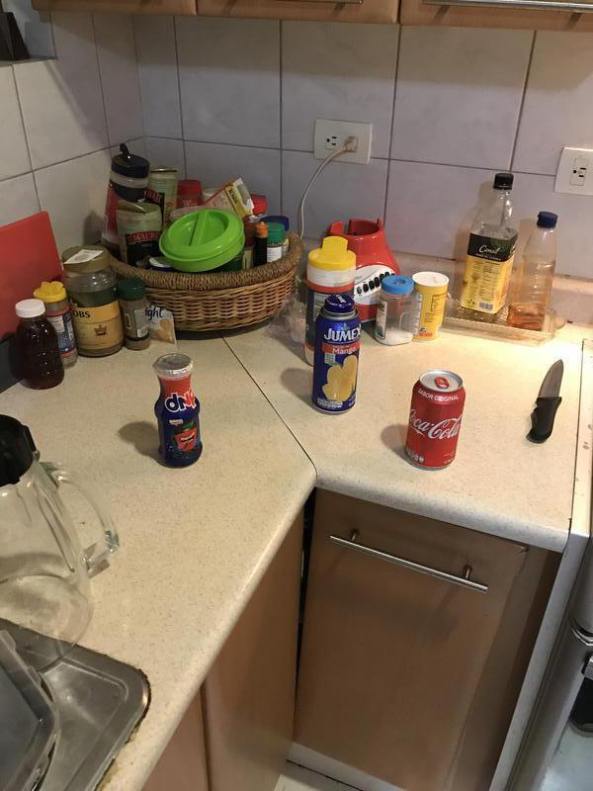
object_detection/test_images/test_image_tf2.jpg
