RoBorregos/robocup-home/catkin_home/src/navigation/base_control/config/yocs_velocity_smoother.yaml

# Example configuration:
# - velocity limits are around a 10% above the physical limits
# - acceleration limits are just low enough to avoid jerking

# Mandatory parameters
speed_lim_v_x: 0.35
speed_lim_v_y: 0.0
speed_lim_w: 0.5

accel_lim_v_x: 0.15
accel_lim_v_y: 0.0
accel_lim_w: 0.2

# Optional parameters
frequency: 20.0
decel_factor: 20.0

# Robot velocity feedback type:
#  0 - none
#  1 - odometry
#  2 - end robot commands
robot_feedback: 0
