RoBorregos/robocup-home/catkin_home/src/navigation/nav_main/config/imu/move_base_params.yaml

shutdown_costmaps: false

controller_frequency: 4.0
controller_patience: 3.0 # 3.0

planner_frequency: 1.0
planner_patience: 3.0

oscillation_timeout: 0.0
oscillation_distance: 0.2

# Planner selection
base_global_planner: "global_planner/GlobalPlanner"  
base_local_planner: "teb_local_planner/TebLocalPlannerROS"

max_planning_retries: 1

recovery_behavior_enabled: true
clearing_rotation_allowed: true

useMagnetometer: false
auto_update_: false
particle_range: 1.0
angle_tolerance: 0.15

recovery_behaviors:
 #- name: 'conservative_reset'
  #  type: 'clear_costmap_recovery/ClearCostmapRecovery'
  - name: 'aggressive_reset'
    type: 'clear_costmap_recovery/ClearCostmapRecovery'
  #- name: 'super_reset'
   # type: 'clear_costmap_recovery/ClearCostmapRecovery'
  - name: 'clearing_rotation'
    type: 'rotate_recovery/RotateRecovery'
  #- name: 'move_slow_and_clear'
    #type: 'move_slow_and_clear/MoveSlowAndClear'
    
conservative_reset:
  reset_distance: 3.0
  #layer_names: [static_layer, obstacle_layer, inflation_layer]
  layer_names: [obstacle_layer]

aggressive_reset:
  reset_distance: 1.0
  #layer_names: [static_layer, obstacle_layer, inflation_layer]
  layer_names: [obstacle_layer]

super_reset:
  reset_distance: 5.0
  #layer_names: [static_layer, obstacle_layer, inflation_layer]
  layer_names: [obstacle_layer]

move_slow_and_clear:
  clearing_distance: 0.5
  limited_trans_speed: 0.1
  limited_rot_speed: 0.4
  limited_distance: 0.3
