RoBorregos/robocup-home/microcontroller/ArmController/nema.h

// nema single step is 1.8° or 0.031 rad. 
void nemaStep(int dirPin,int stepPin, bool clockWise){
  //Activar una direccion y fijar la velocidad con stepDelay
  if(clockWise == true){
      digitalWrite(dirPin, HIGH); 
  }else{
    digitalWrite(dirPin, LOW);
  }
  const int stepDelay = 250;
  digitalWrite(stepPin, HIGH);
  delayMicroseconds(stepDelay);
  digitalWrite(stepPin, LOW);
  delayMicroseconds(stepDelay);
}

void testNema(int dirPin, int stepPin){
    const int stepDelay = 2500;
    digitalWrite(dirPin, LOW); 

  for(int i = 0; i<3000; i++){
    digitalWrite(stepPin, HIGH);
    delayMicroseconds(stepDelay);
    digitalWrite(stepPin, LOW);
    delayMicroseconds(stepDelay);
  }
  delay(2000);
  digitalWrite(dirPin, LOW); 
}
